shlokdee/macro9000/schematic/macro9000.kicad_sch

## KiCad design schematic/macro9000.kicad_sch (2026-10-07)

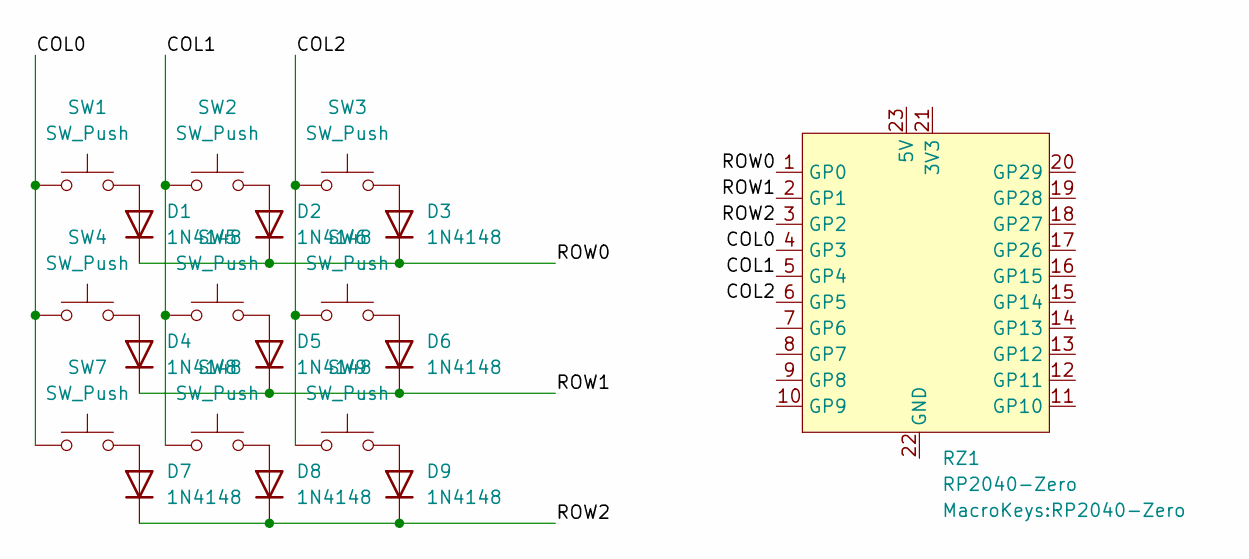
[picture p7: schematic macro9000.kicad_sch]

Parts:
D1, D2, D3, D4, D5, D6, D7, D8, D9: 1N4148; D_DO-35_SOD27_P7.62mm_Horizontal
RZ1: RP2040-Zero
SW1, SW2, SW3, SW4, SW5, SW6, SW7, SW8, SW9: SW_Push; Nidec_Copal_CAS-120A

Connections:
COL0: RZ1.4 (GP3), SW1.1, SW4.1, SW7.1
COL1: RZ1.5 (GP4), SW2.1, SW5.1, SW8.1
COL2: RZ1.6 (GP5), SW3.1, SW6.1, SW9.1
unnamed: D1.2 (A), SW1.2
unnamed: D2.2 (A), SW2.2
unnamed: D3.2 (A), SW3.2
unnamed: D4.2 (A), SW4.2
unnamed: D5.2 (A), SW5.2
unnamed: D6.2 (A), SW6.2
unnamed: D7.2 (A), SW7.2
unnamed: D8.2 (A), SW8.2
unnamed: D9.2 (A), SW9.2
ROW0: D1.1 (K), D2.1 (K), D3.1 (K), RZ1.1 (GP0)
ROW1: D4.1 (K), D5.1 (K), D6.1 (K), RZ1.2 (GP1)
ROW2: D7.1 (K), D8.1 (K), D9.1 (K), RZ1.3 (GP2)
